gav-/PaperTapeReader/images/02-Tape reader holes.jpg

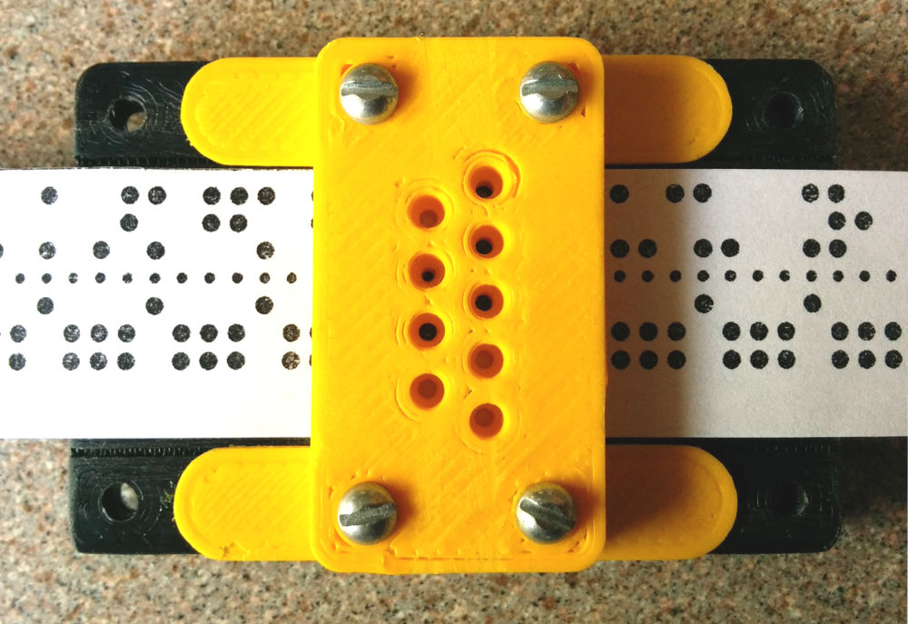
images/02-Tape reader holes.jpg
