gav-/PaperTapeReader/images/05-Emitter board.jpg

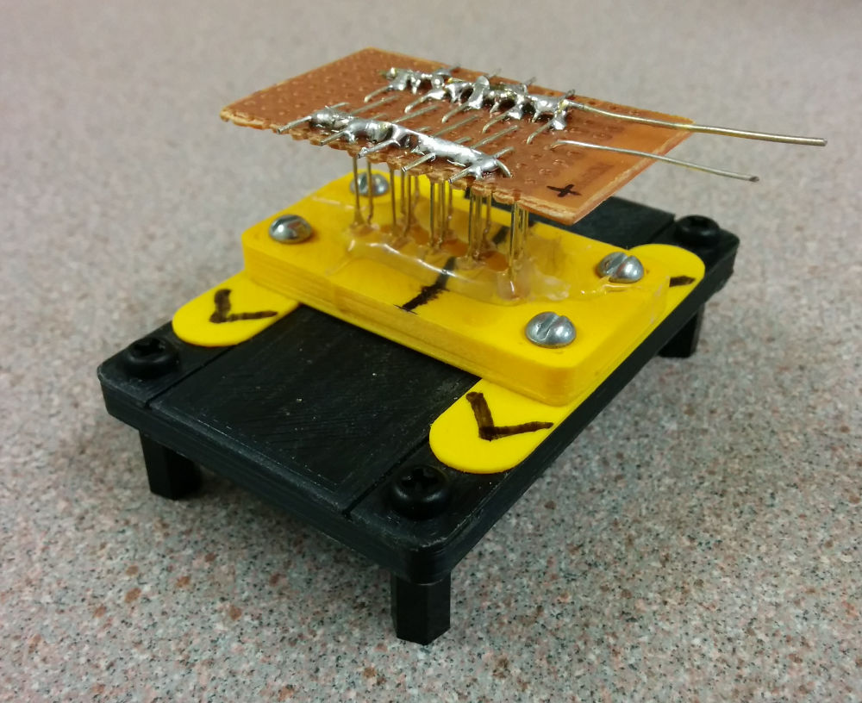
images/05-Emitter board.jpg
