gav-/PaperTapeReader/images/06-Base holes.jpg

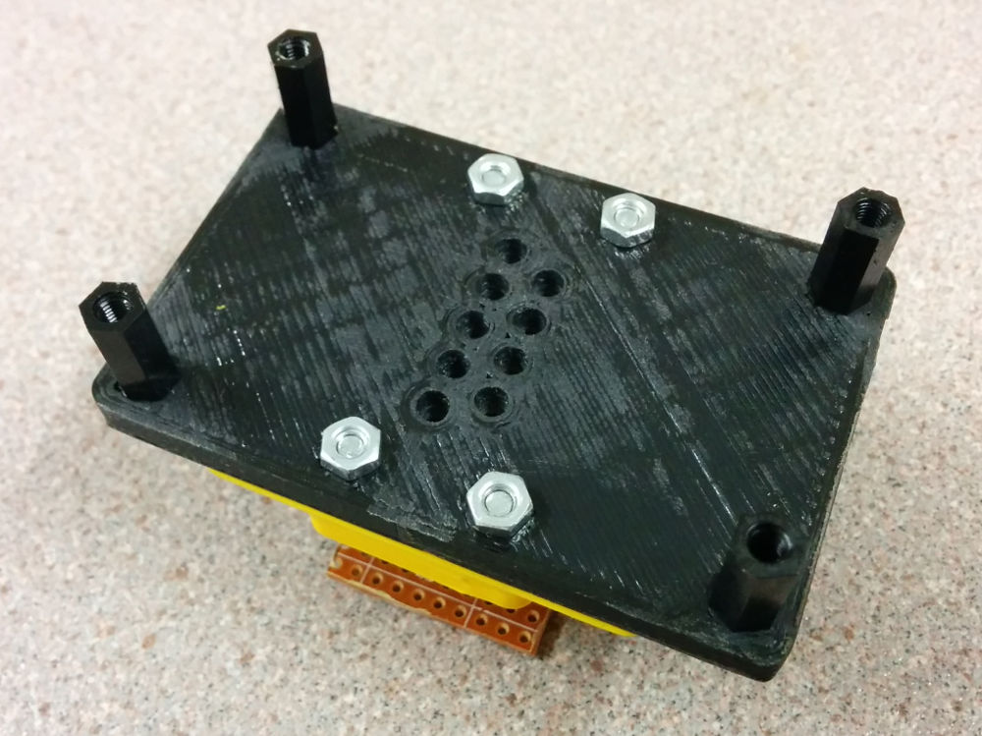
images/06-Base holes.jpg
