gav-/PaperTapeReader/images/07-IR emission through base holes.jpg

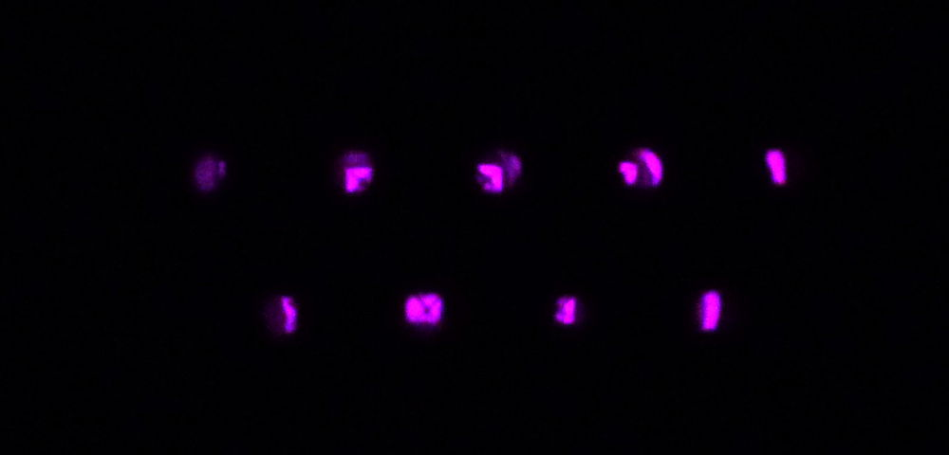
images/07-IR emission through base holes.jpg
